ChrisMicro/freiBot/eagle/freiBotSchaltplan20151025_1.png

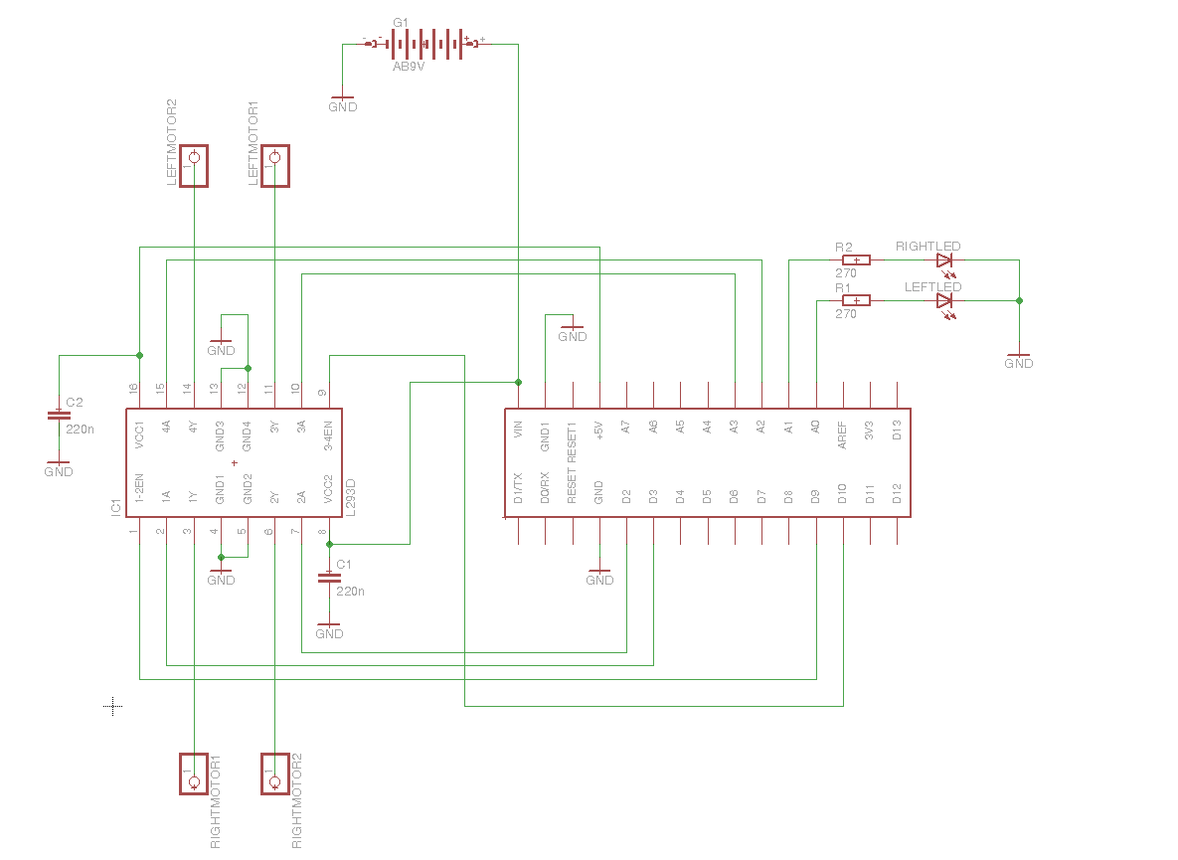
eagle/freiBotSchaltplan20151025_1.png
